zqazi114/SEA/Cadence/SMA_fabA/layout/Fab/TOP.pdf

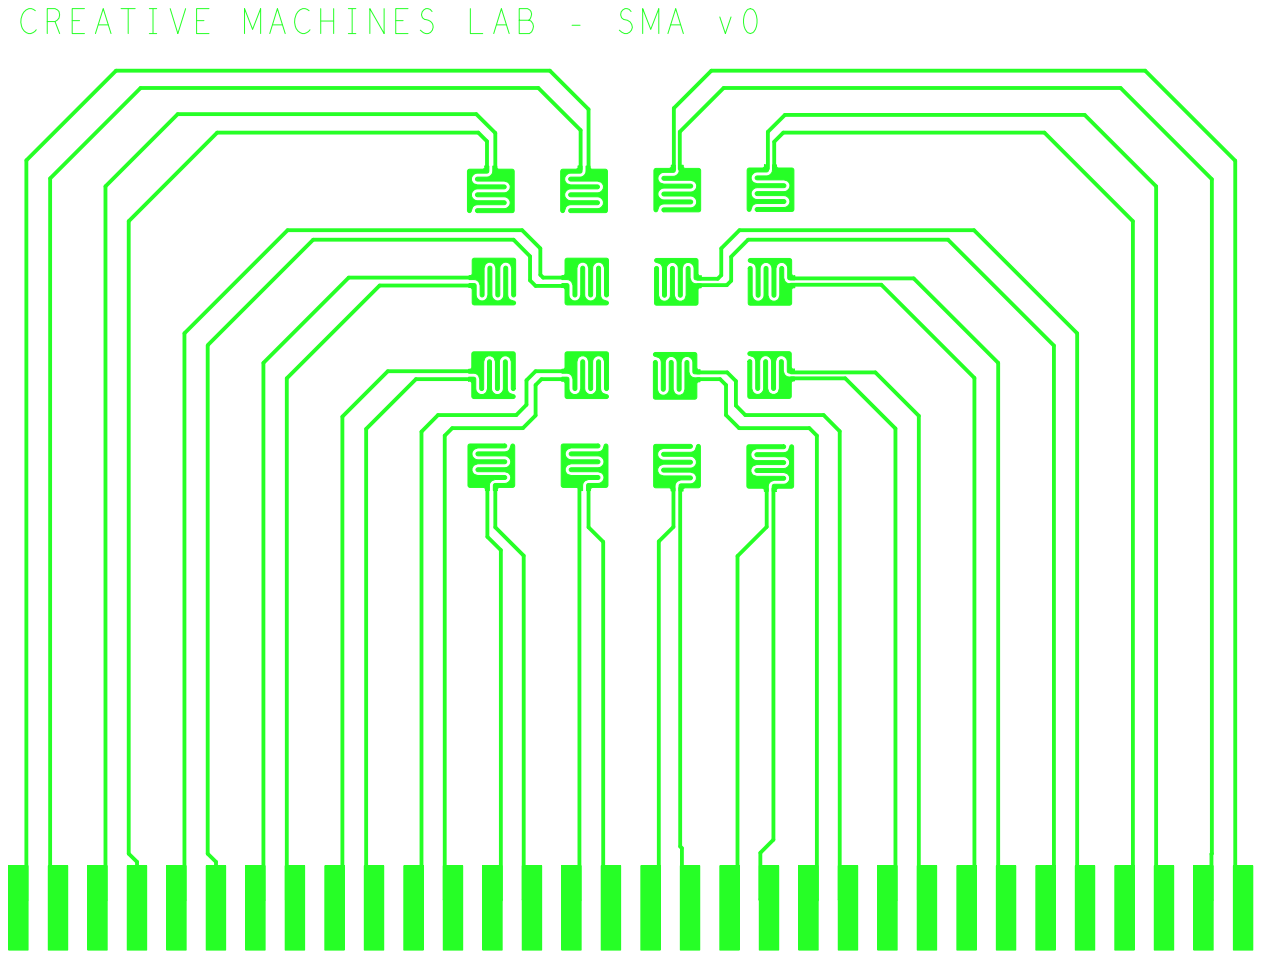
[picture p50: page 1]
